Hdchipeo/NexusIR/docs/Huong_Dan_Set_Up_HomeKit_Lamp.pdf

# HƯỚNG DẪN CÀI ĐẶT ĐÈN HOMEKIT

Tài liệu hướng dẫn kết nối mạng Wi-Fi và đồng bộ Apple HomeKit rút gọn

## 1. Chuẩn Bị Trước Khi Cài Đặt

- Mạng Wi-Fi 2.4GHz: Bắt buộc kết nối điện thoại vào Wi-Fi 2.4GHz (không dùng mạng 5GHz).
- Điện thoại iPhone: Đã cài sẵn ứng dụng Home (Nhà) và bật sẵn Bluetooth, định vị.

## 2. Phần I: Cấu Hình Wi-Fi Cho Thiết Bị (Wi-Fi Provisioning)

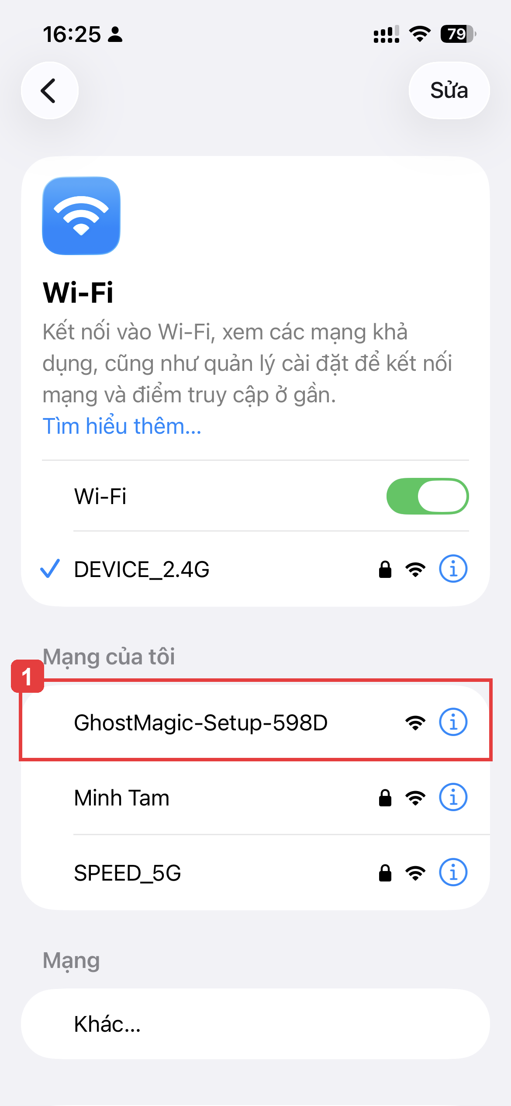
[picture p19: figure]

Bước 1

Mở cài đặt Wi-Fi trên iPhone.

Tìm và chọn mạng Wi-Fi do thiết bị phát ra có tên định dạng: GhostMagic-Setup-xxxx (trong ảnh là GhostMagic-Setup-598D).

© 2026 NexusIR. Hướng dẫn thiết lập rút gọn. | Trang 1 / 7

Bước 2

Chờ kết nối thành công với Wi-Fi của thiết bị (hiển thị dấu tích xanh ở đầu).

Lưu ý: Dưới tên Wi-Fi sẽ ghi cảnh báo mạng không bảo mật hoặc không có internet, điều này là bình thường.

Bước 3

Màn hình đăng nhập mạng Captive Portal (Wi-Fi xác thực) sẽ tự động hiển thị.

Tại danh sách Wi-Fi hiện ra, chọn đúng mạng Wi-Fi nhà bạn (băng tần 2.4GHz, ví dụ là DEVICE_2.4G).

Hướng Dẫn Thiết Lập Đèn HomeKit - NexusIR

Bước 4

Nhập chính xác mật khẩu Wi-Fi nhà bạn vào ô trống (4a).

Sau đó nhấn nút Join (4b) ở góc dưới bên phải hộp thoại để lưu cấu hình.

Bước 5

Chờ thiết bị lưu cấu hình và tự khởi động lại.

Màn hình sẽ hiển thị thông báo toast màu đen ở chân trang: Success! Rebooting... báo hiệu thành công.

Thiết bị sẽ tự kết nối vào mạng Wi-Fi nhà bạn.

## 3. Phần II: Đồng Bộ Với Apple HomeKit (HomeKit Pairing)

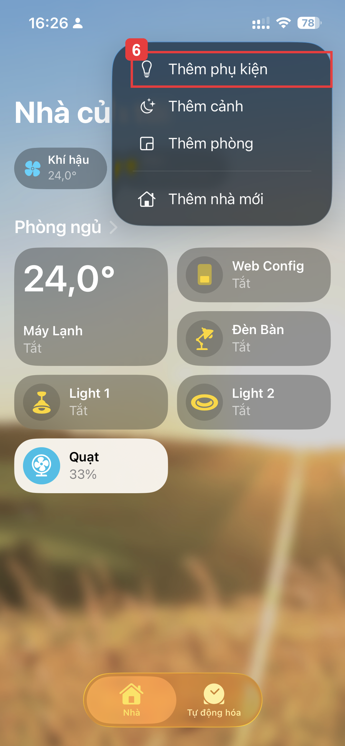
[picture p20: figure]

Bước 6

Mở ứng dụng Home (Nhà) trên iPhone.

Nhấn vào biểu tượng dấu (+) ở góc trên cùng bên phải và chọn Thêm phụ kiện (Add Accessory).

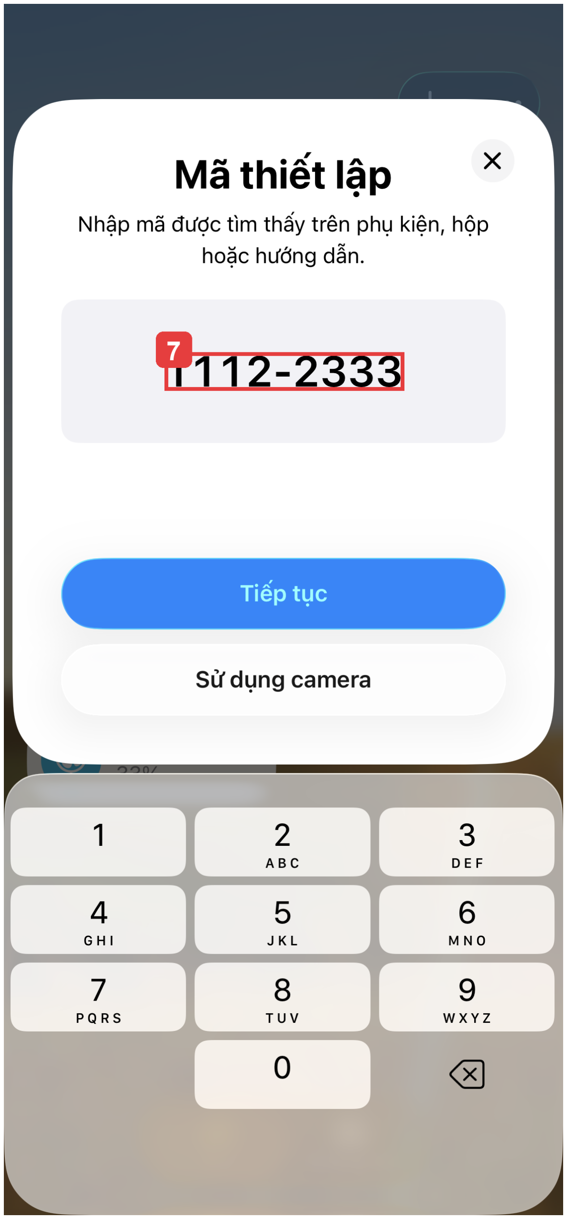
[picture p21: figure]

Bước 7

Giao diện quét mã hiện lên, chọn 'Tôi không có mã hoặc không thể quét' hoặc 'Thêm bằng mã...'.

Tiến hành nhập mã cài đặt 8 số của HomeKit: 111-22-333 (nhập liền 11122333).

Bước 8

Khi xuất hiện hộp thoại cảnh báo phụ kiện chưa được chứng nhận từ Apple.

Hãy chọn nút Vẫn thêm (Add Anyway) ở phía bên trái để tiếp tục tiến trình đồng bộ.

Bước 9

Chờ quá trình kết nối cầu nối của thiết bị hoàn tất (màn hình hiển thị Đang thêm vào màn hình chính...).

Sau đó, chọn Tiếp tục ở phía dưới cùng màn hình.

Bước 10

Đặt tên tùy chỉnh cho Cầu nối (ví dụ: GhostLamp Bridge) và gán phòng tương ứng.

Sau đó, chọn Tiếp tục (nhấn Xác định/Tiếp tục cho các thiết bị phụ trợ liên kết).

Bước 11

Hệ thống báo đã thêm thành công phụ kiện đèn thông minh vào Nhà.

Nhấn chọn Xong (Done) ở góc dưới cùng để hoàn tất quá trình cài đặt và bắt đầu sử dụng.

## 4. Phần III: Giao Diện Điều Khiển

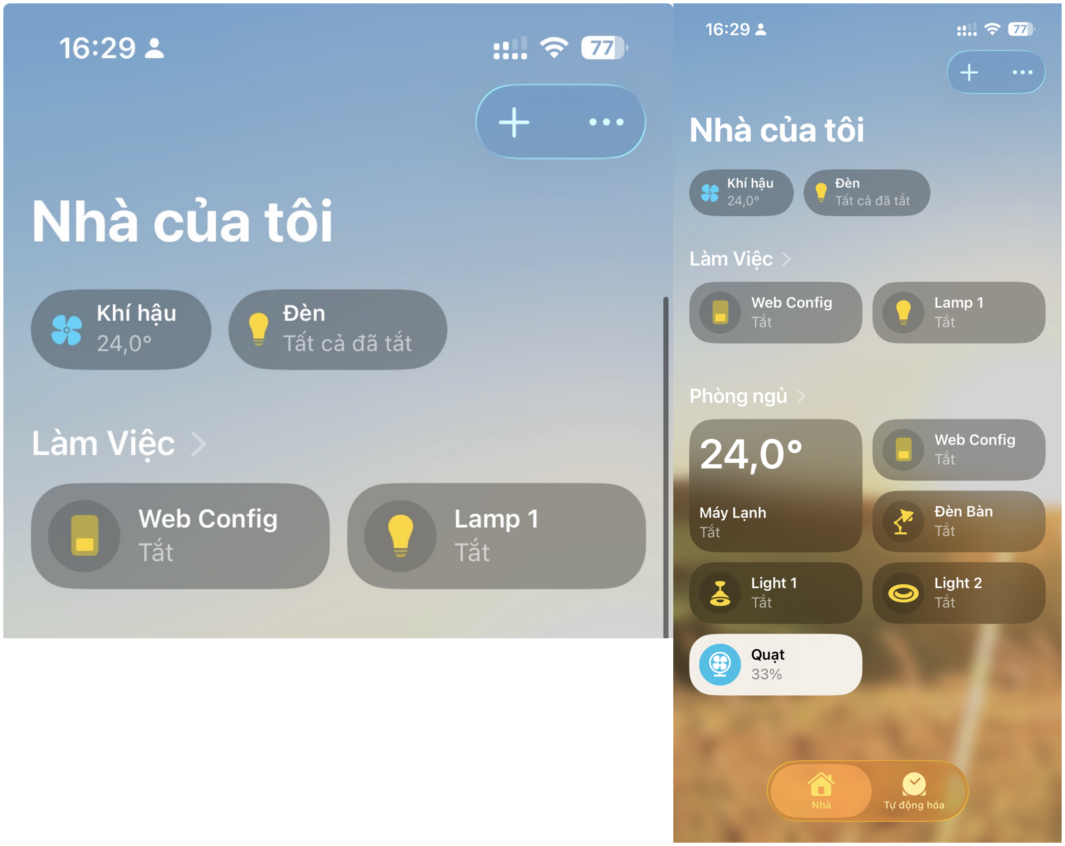
[picture p22: figure]

Bảng điều khiển sau khi cài đặt:

- Thiết bị hiển thị dưới dạng cầu nối GhostLamp Bridge quản lý đèn LED và các cảm biến phụ trợ.
- Cho phép điều khiển bật/tắt nhanh, tùy chọn độ sáng, bảng màu sắc RGB đầy đủ của đèn LED.
- Nút Web Config dùng để kích hoạt nhanh trang cấu hình web cục bộ của thiết bị.

## 5. Hướng Dẫn Khắc Phục Sự Cố (Troubleshooting)

Vấn đề thường gặp | Giải pháp xử lý
Không thấy Wi-Fi GhostMagic-Setup-xxxx | 1. Kiểm tra nguồn cấp. 2. Để reset thiết bị về mặc định: Nhấn giữ button vật lý trên thiết bị trong 3 giây cho đến khi đèn nháy để vào chế độ Setup.
Trang cấu hình Wi-Fi không tự hiển thị | Đảm bảo điện thoại đã kết nối Wi-Fi thiết bị. Mở trình duyệt và truy cập tên miền mDNS: http://ghostmagic.local:8080 để mở cấu hình.
Đèn không kết nối được vào Wi-Fi nhà | Yêu cầu Wi-Fi nhà phải là mạng 2.4GHz. Đảm bảo nhập đúng mật khẩu mạng Wi-Fi.
