Hdchipeo/NexusIR/picture/IMG_3901.PNG

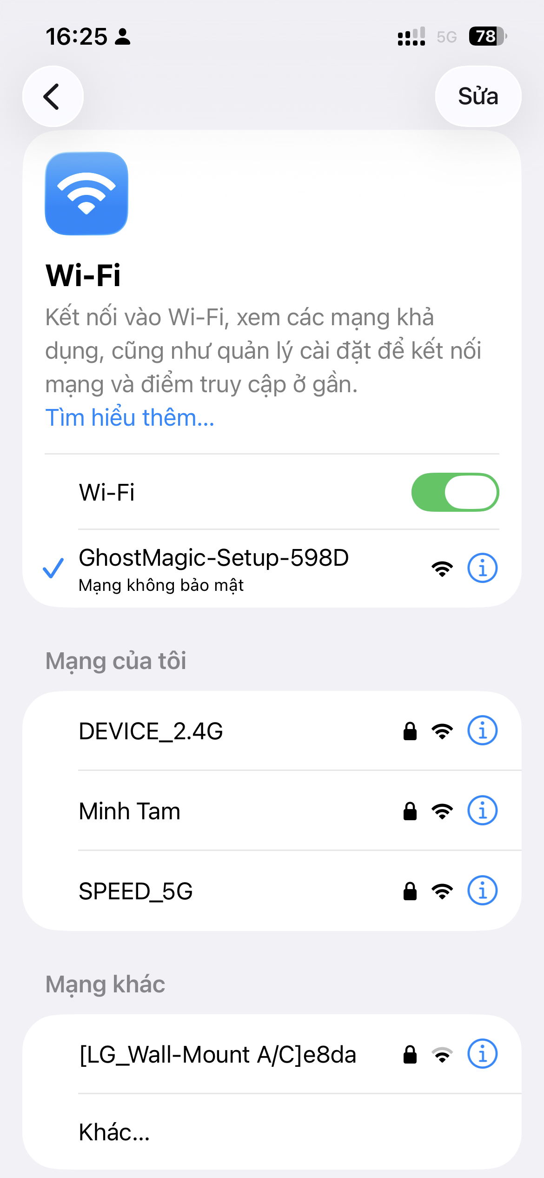
picture/IMG_3901.PNG
