Hdchipeo/NexusIR/picture/IMG_3903.PNG

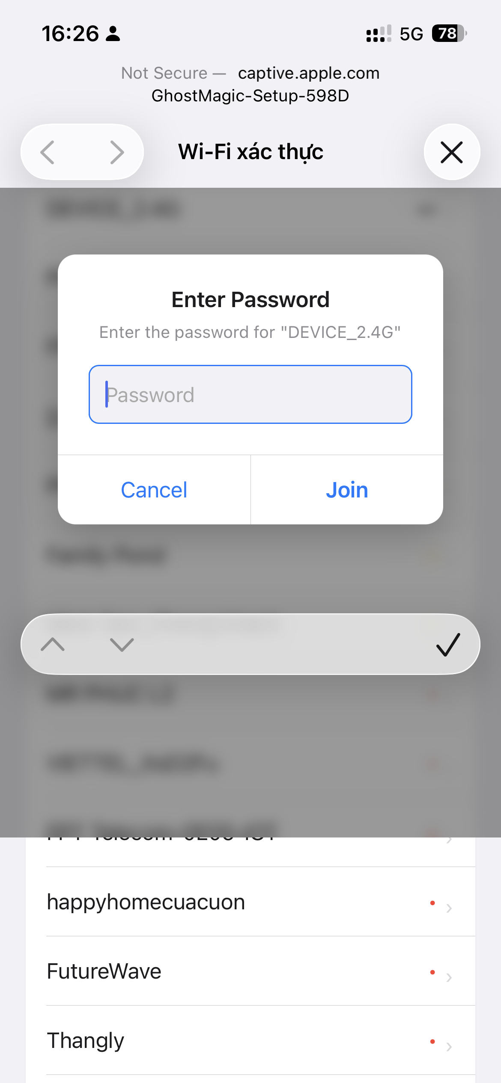
picture/IMG_3903.PNG
