Hdchipeo/NexusIR/picture/IMG_3905.PNG

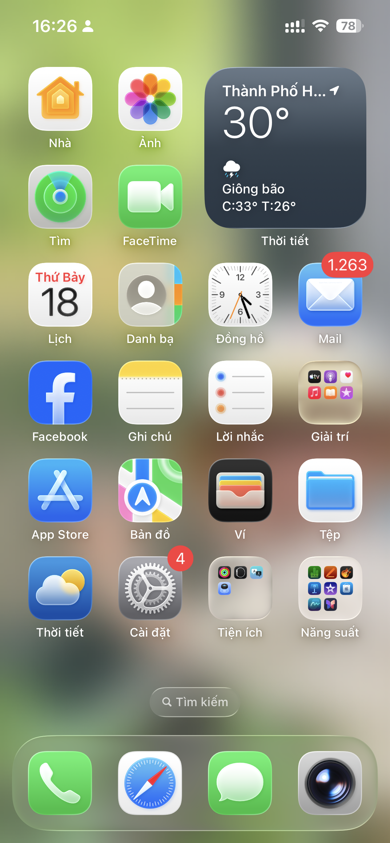
picture/IMG_3905.PNG
