Hdchipeo/NexusIR/picture/IMG_3906.PNG

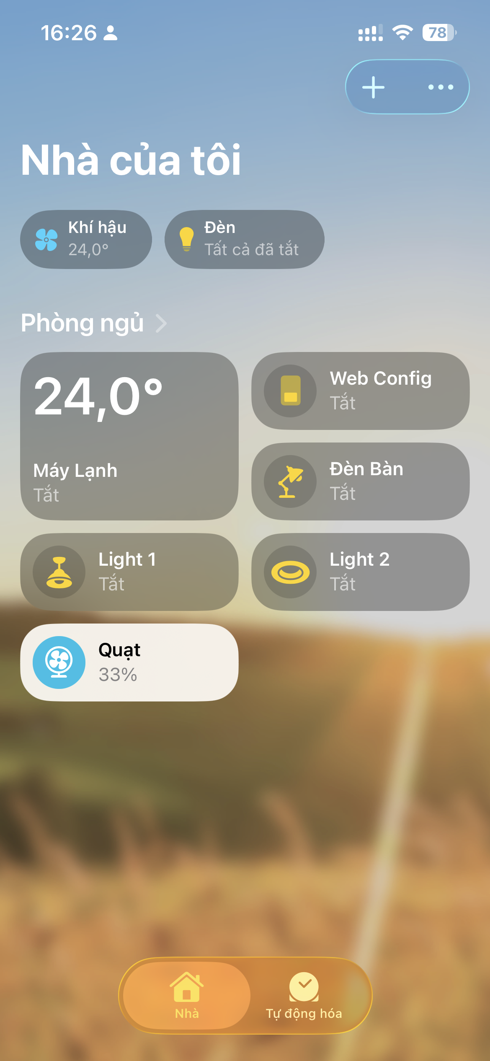
picture/IMG_3906.PNG
