Hdchipeo/NexusIR/picture/IMG_3908.PNG

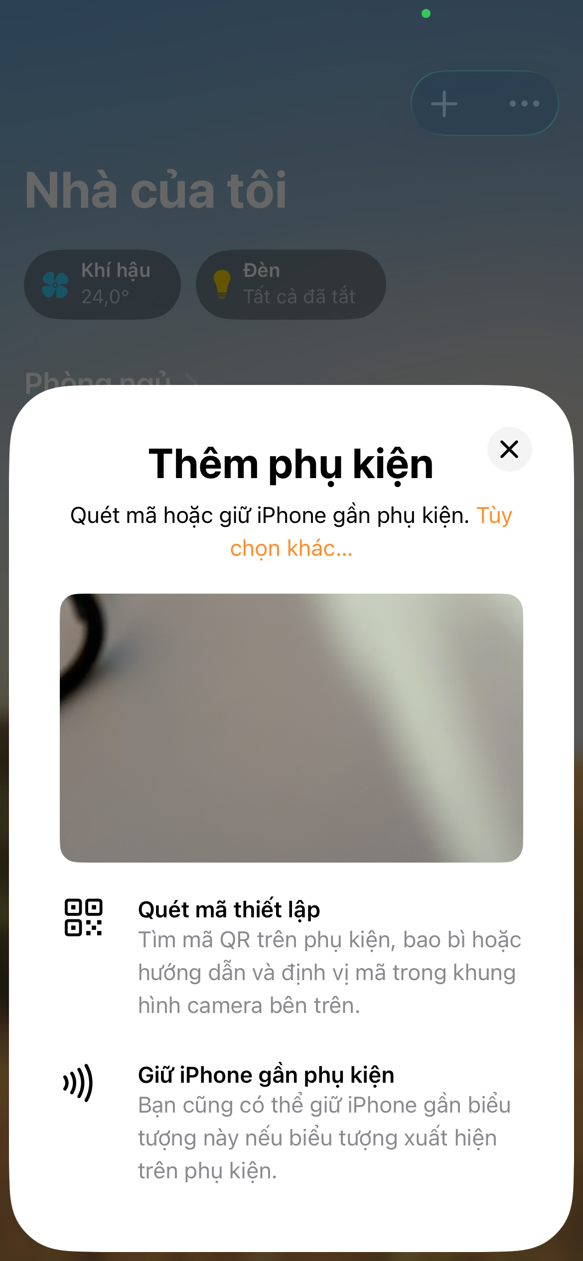
picture/IMG_3908.PNG
