Hdchipeo/NexusIR/picture/IMG_3909.PNG

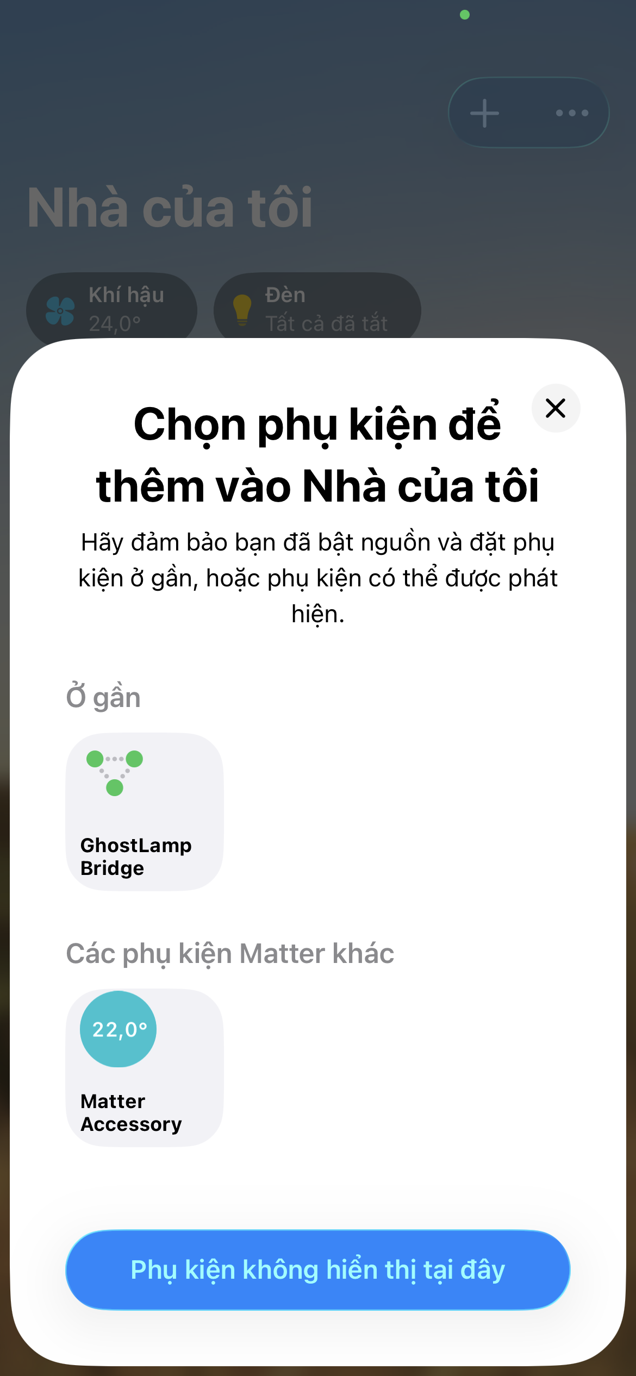
picture/IMG_3909.PNG
