Hdchipeo/NexusIR/picture/IMG_3911.PNG

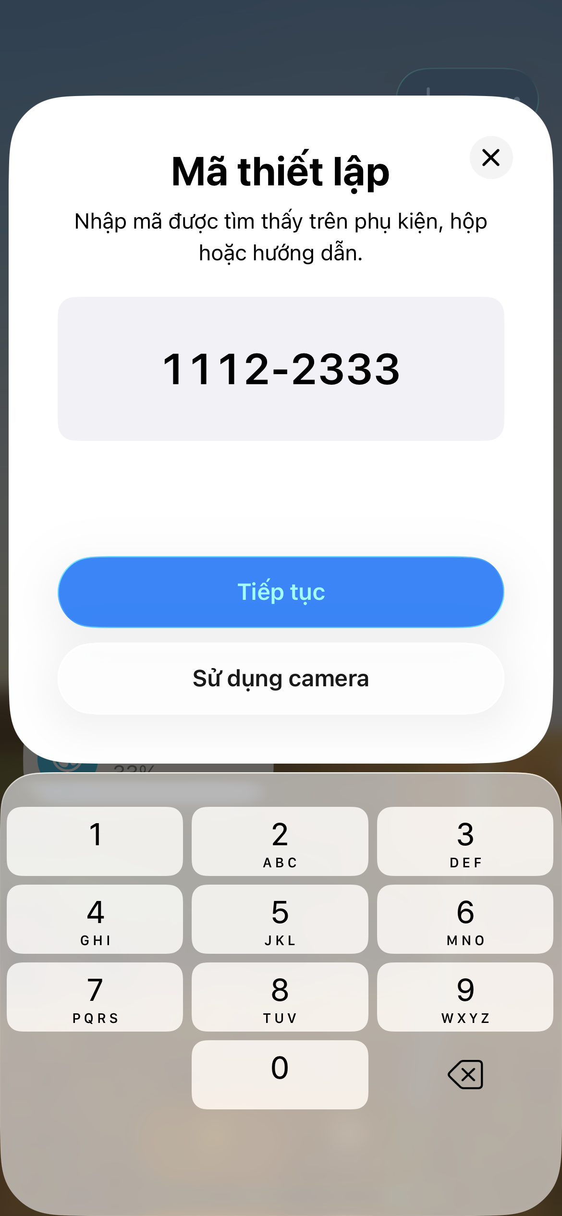
picture/IMG_3911.PNG
