Hdchipeo/NexusIR/picture/IMG_3912.PNG

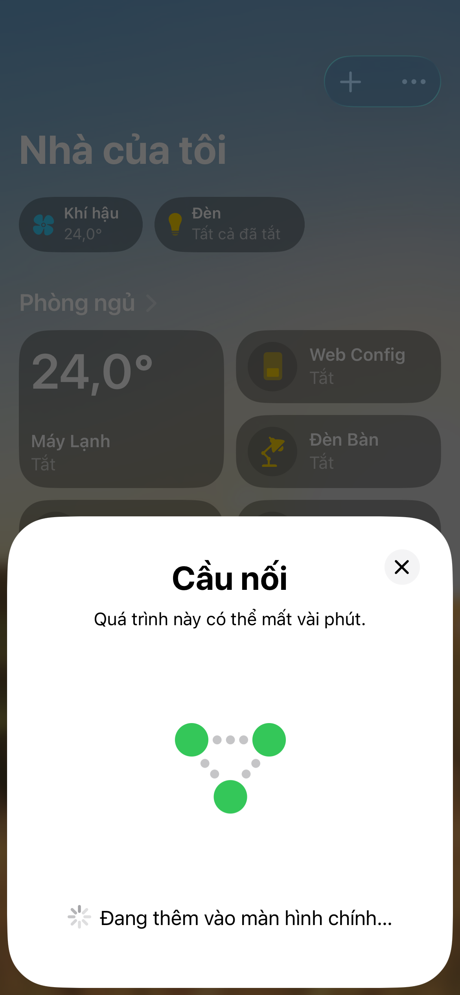
picture/IMG_3912.PNG
