Hdchipeo/NexusIR/picture/IMG_3913.PNG

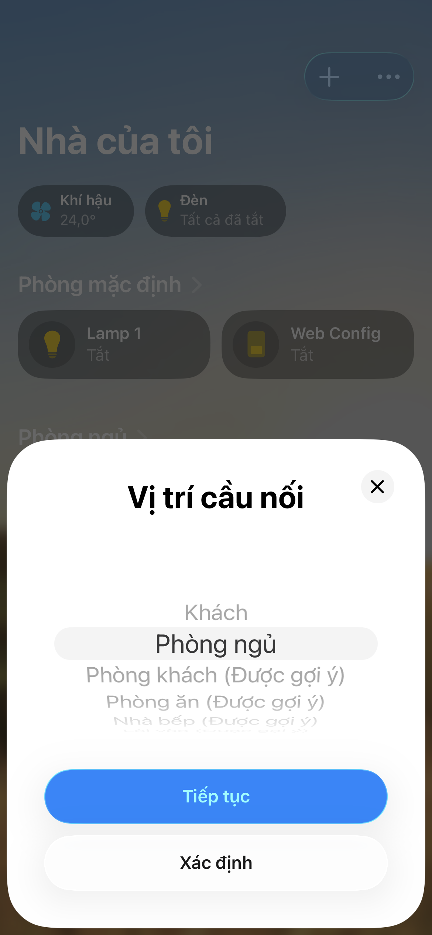
picture/IMG_3913.PNG
