Hdchipeo/NexusIR/picture/IMG_3914.PNG

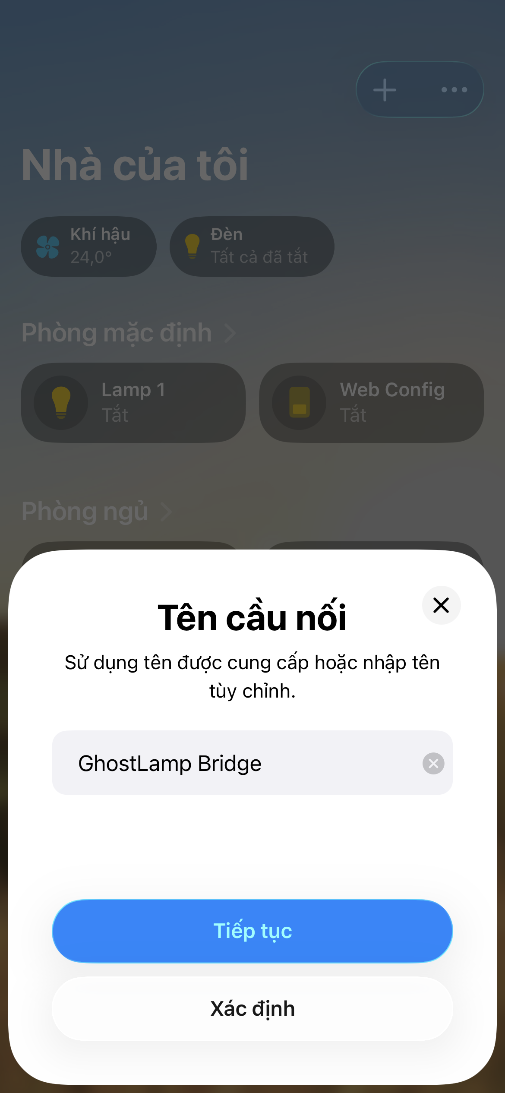
picture/IMG_3914.PNG
