Hdchipeo/NexusIR/picture/IMG_3915.PNG

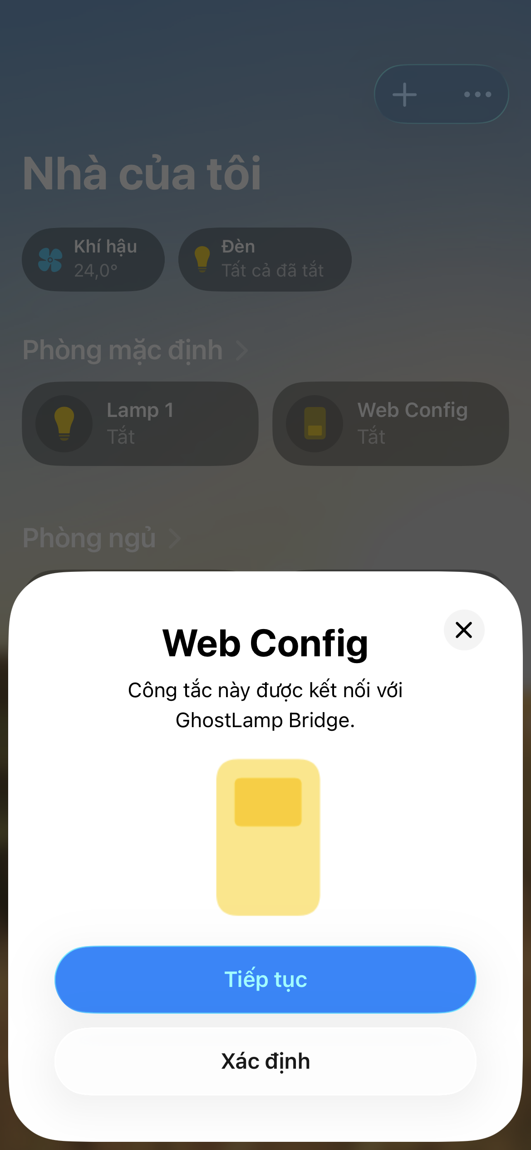
picture/IMG_3915.PNG
