Hdchipeo/NexusIR/docs/images/step1_grid.png

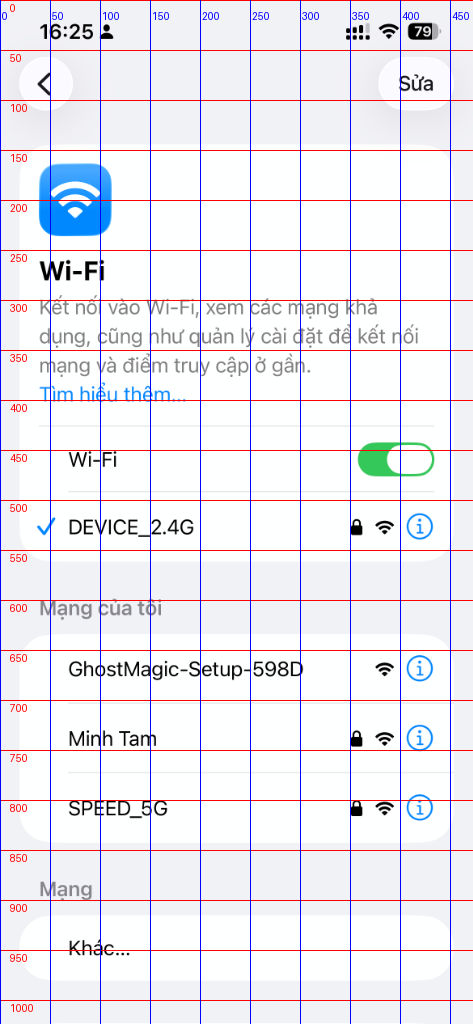
docs/images/step1_grid.png
