Hdchipeo/NexusIR/docs/images/step5_raw.png

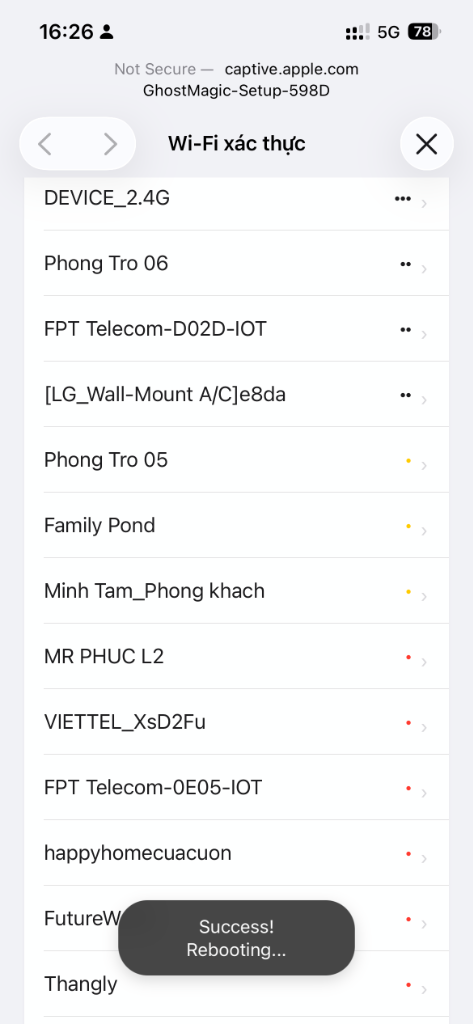
docs/images/step5_raw.png
