Hdchipeo/NexusIR/docs/images/step7_annotated.png

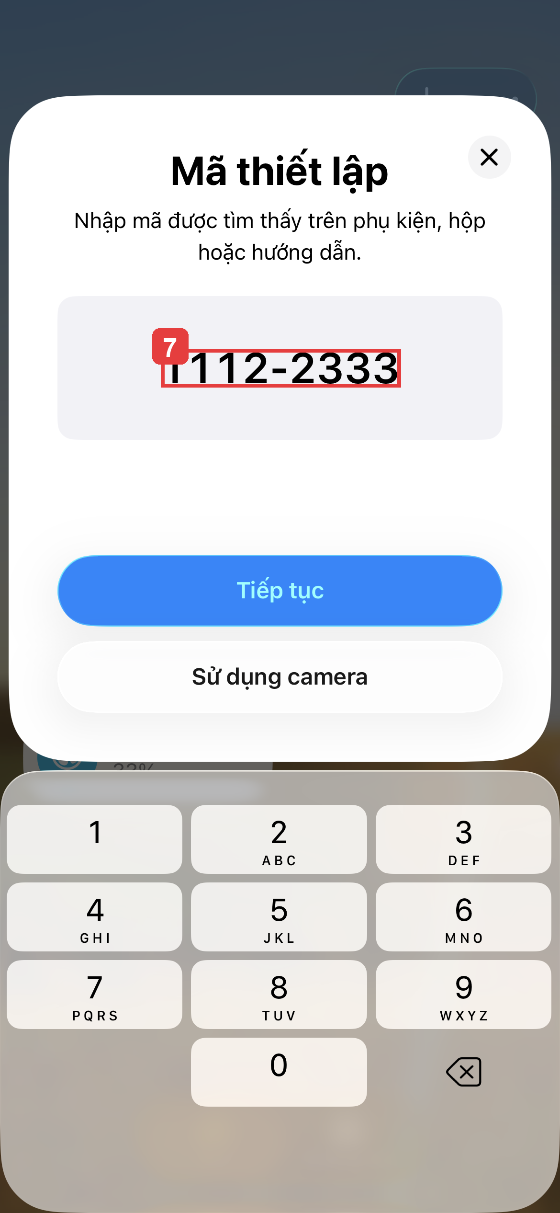
docs/images/step7_annotated.png
