Hdchipeo/NexusIR/docs/images/step8_annotated.png

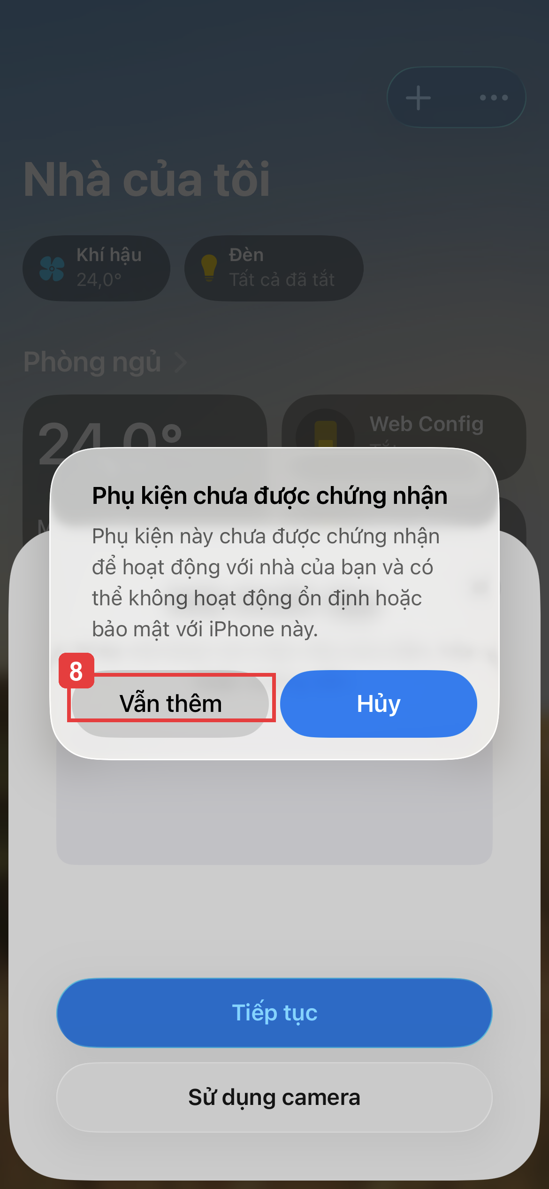
docs/images/step8_annotated.png
