Hdchipeo/NexusIR/docs/images/step11_annotated.png

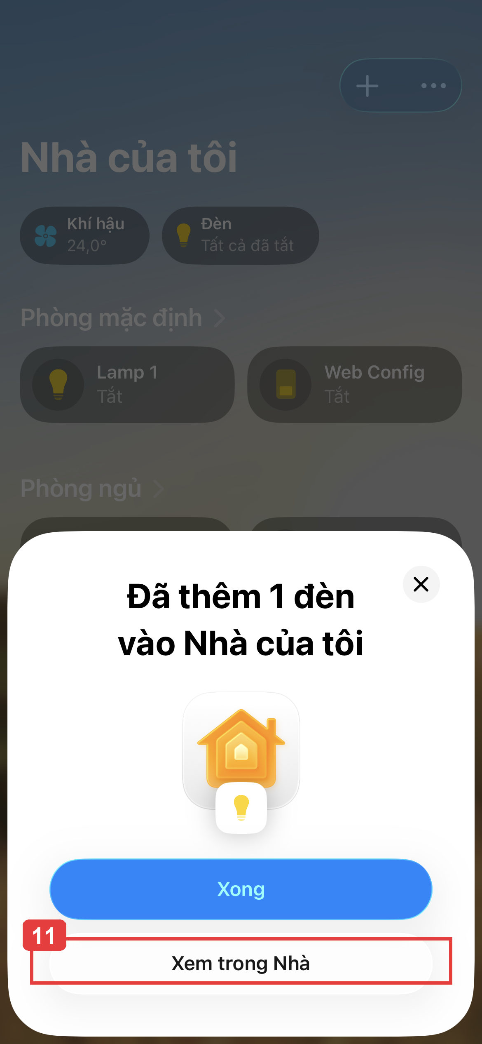
docs/images/step11_annotated.png
