Hdchipeo/NexusIR/hardware/3d_print/anh2.png

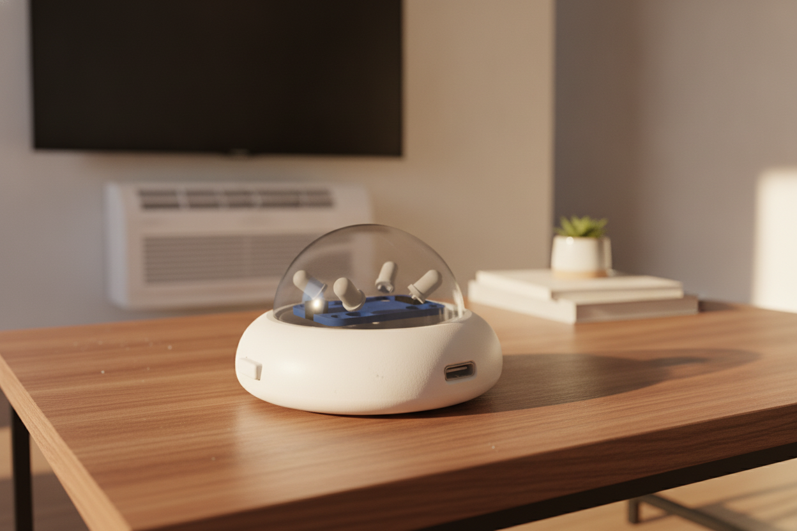
hardware/3d_print/anh2.png
