Hdchipeo/NexusIR/hardware/3d_print/anh3.png

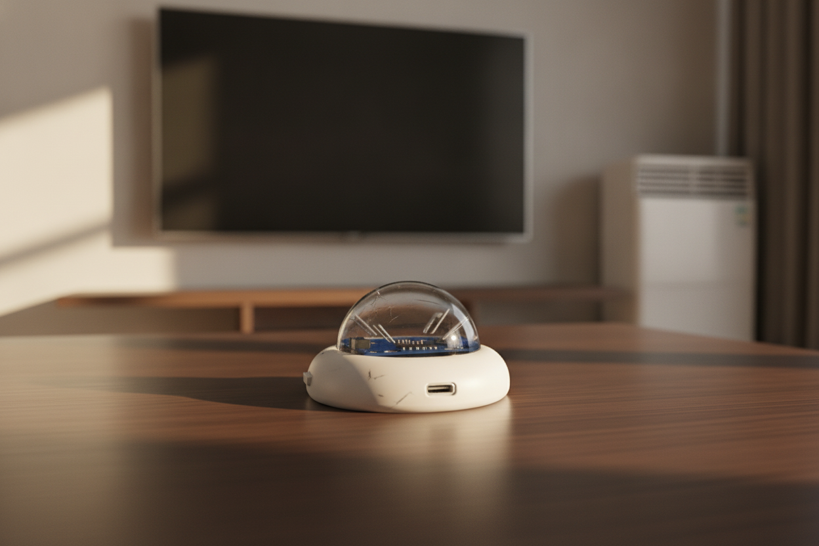
hardware/3d_print/anh3.png
