Hdchipeo/NexusIR/hardware/3d_print/case2.png

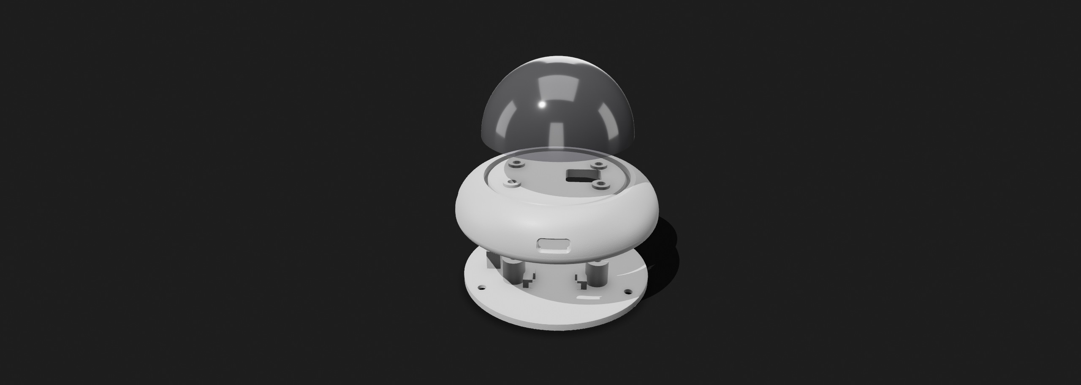
hardware/3d_print/case2.png
