Hdchipeo/NexusIR/hardware/3d_print/Case.png

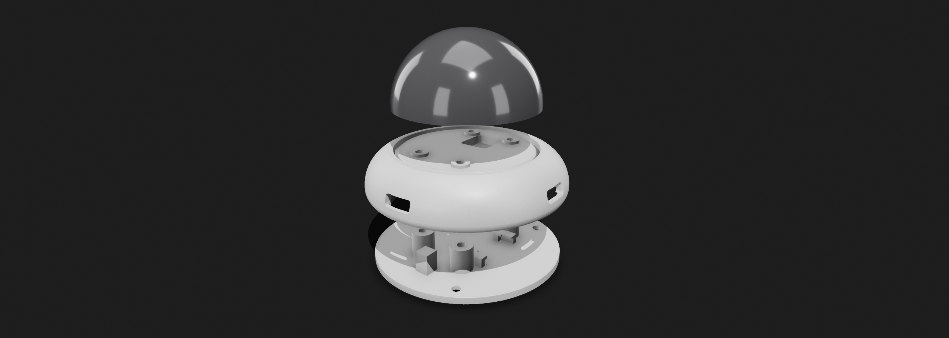
hardware/3d_print/Case.png
