Hdchipeo/NexusIR/hardware/3d_print/Gemini_Generated_Image_agxx58agxx58agxx.png

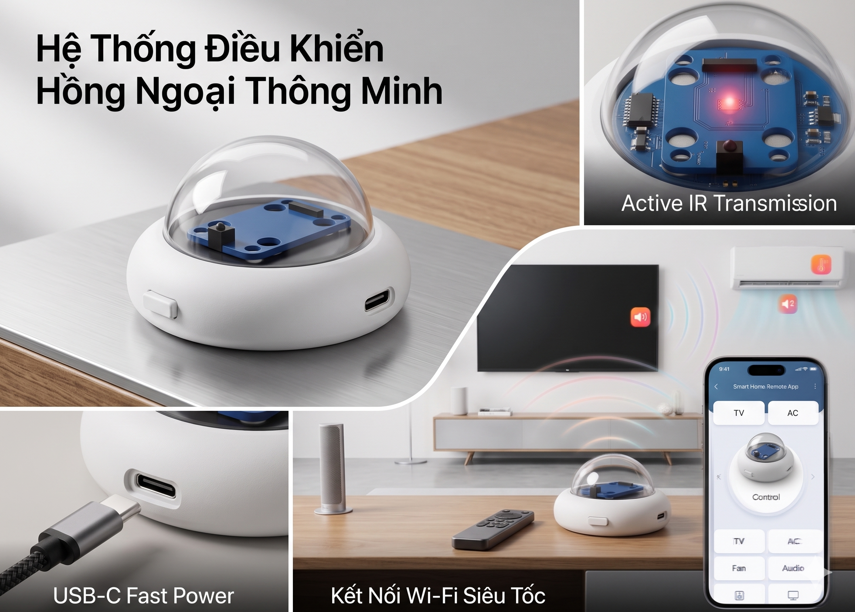
hardware/3d_print/Gemini_Generated_Image_agxx58agxx58agxx.png
