Hdchipeo/NexusIR/hardware/3d_print/Gemini_Generated_Image_dbegdzdbegdzdbeg.png

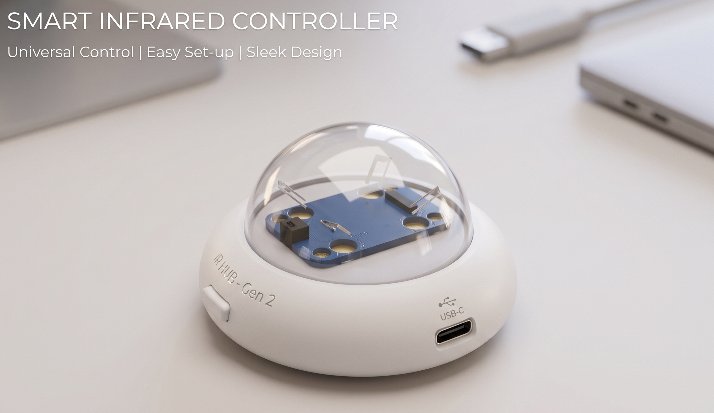
hardware/3d_print/Gemini_Generated_Image_dbegdzdbegdzdbeg.png
