Hdchipeo/NexusIR/hardware/3d_print/Gemini_Generated_Image_hwgq0hwgq0hwgq0h.png

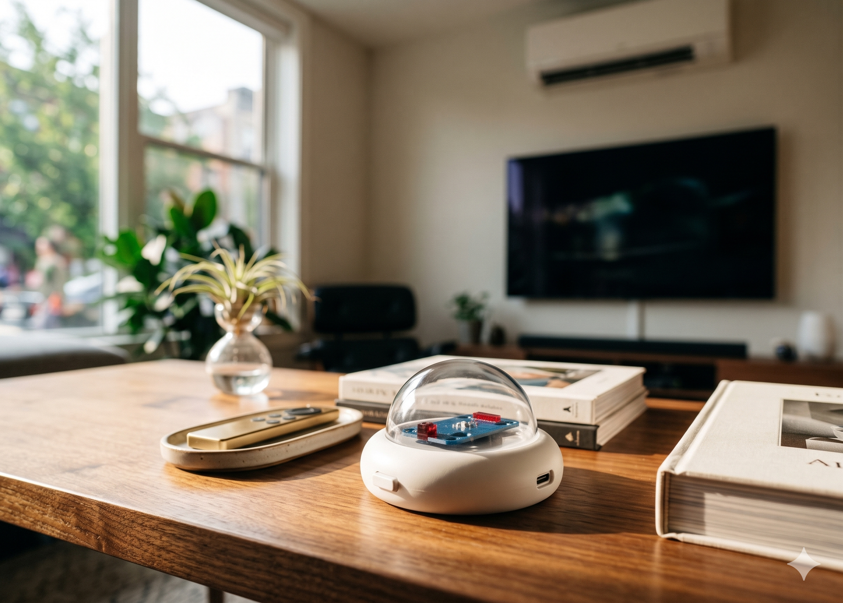
hardware/3d_print/Gemini_Generated_Image_hwgq0hwgq0hwgq0h.png
