Hdchipeo/NexusIR/hardware/3d_print/Untitled.png

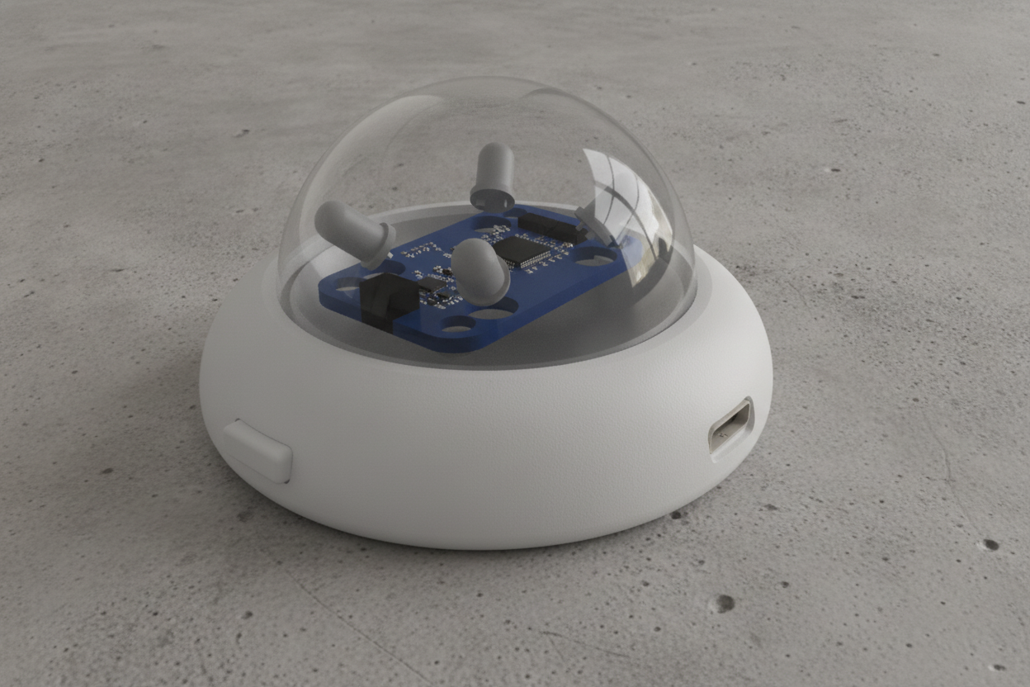
hardware/3d_print/Untitled.png
