Hdchipeo/NexusIR/components/mgr_ir_protocols/include/ir_engine.h

/**
 * @file ir_engine.h
 * @brief Low-level IR Engine (RMT Driver)
 */

#pragma once

#include "esp_err.h"
#include "ir_types.h"

#ifdef __cplusplus
extern "C" {
#endif

/**
 * @brief Initialize the IR Engine (TX Channel)
 *
 * @param config Configuration struct
 * @return esp_err_t ESP_OK on success
 */
esp_err_t ir_engine_init(const ir_engine_config_t *config);

/**
 * @brief Send raw RMT symbols
 *
 * @param symbols Pointer to RMT symbols
 * @param count Number of symbols
 * @return esp_err_t ESP_OK on success
 */
esp_err_t ir_engine_send_raw(const void *symbols, size_t count);

#ifdef __cplusplus
}
#endif
