Hdchipeo/NexusIR/components/drv_aht20/include/drv_aht20.h

#pragma once

#include "esp_err.h"

#ifdef __cplusplus
extern "C" {
#endif

/**
 * @brief Initialize AHT20 Sensor
 *
 * Uses I2C configuration from Kconfig.
 *
 * @return ESP_OK on success
 */
esp_err_t drv_aht20_init(void);

/**
 * @brief Read Temperature and Humidity
 *
 * @param[out] temp Temperature in Celsius
 * @param[out] hum Humidity in %
 * @return ESP_OK on valid read
 */
esp_err_t aht20_sensor_read(float *temp, float *hum);

#ifdef __cplusplus
}
#endif
